zero-pidi-box/PIDI-BOX01-X-ZERO/FOTOS and 3D/3TE-displ-mounting1.jpg

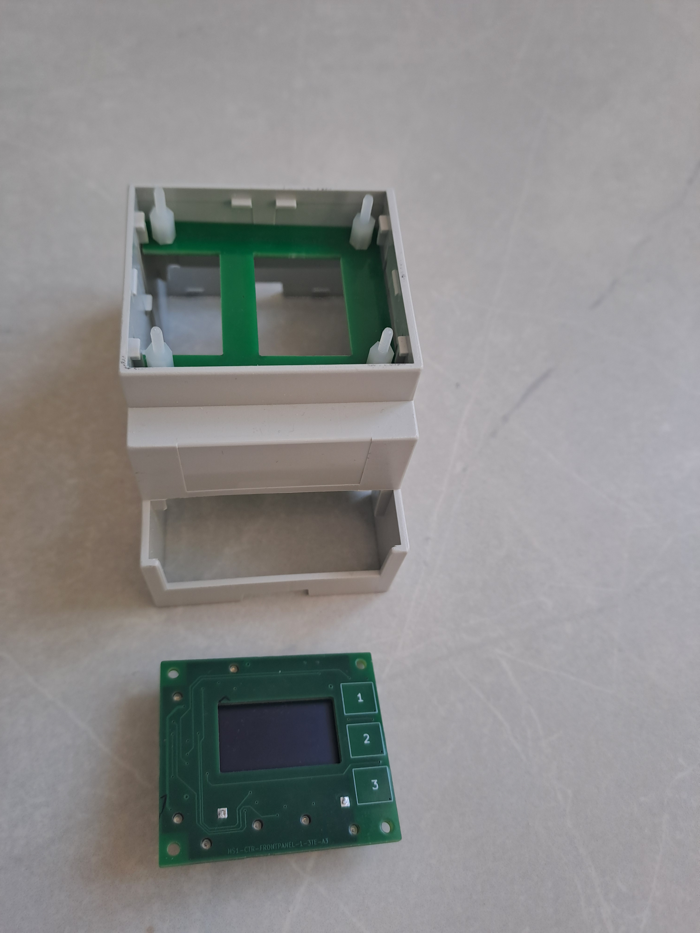
FOTOS and 3D/3TE-displ-mounting1.jpg
