zero-pidi-box/PIDI-BOX01-X-ZERO/FOTOS and 3D/3TE-displ-mounting 3.jpg

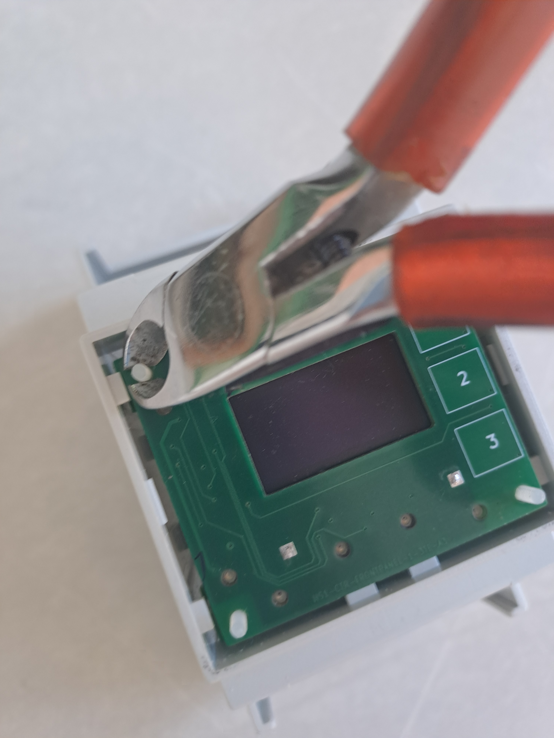
FOTOS and 3D/3TE-displ-mounting 3.jpg
