zero-pidi-box/PIDI-BOX01-X-ZERO/FOTOS and 3D/6 DIG-IN opto.jpg

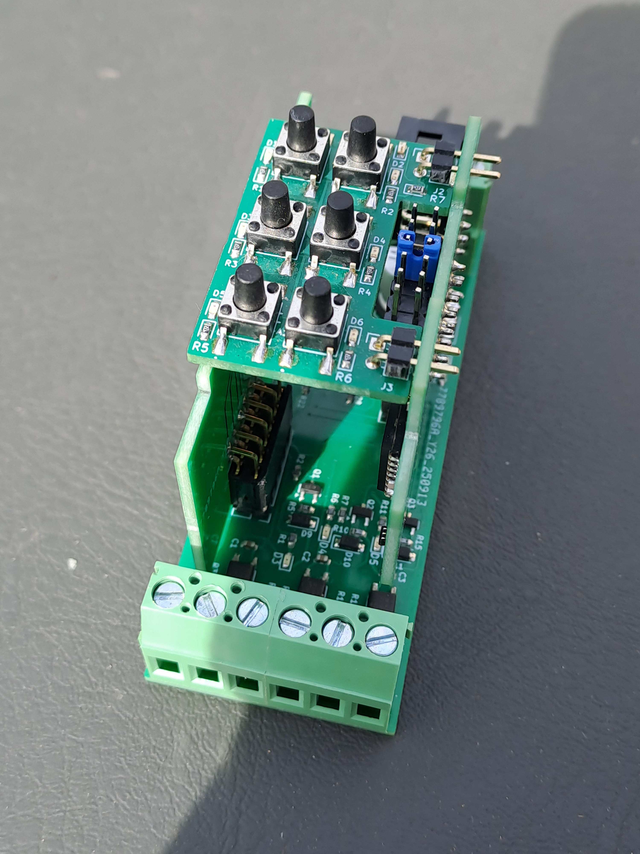
FOTOS and 3D/6 DIG-IN opto.jpg
