zero-pidi-box/PIDI-BOX01-X-ZERO/FOTOS and 3D/6 RELAYS OUT.jpg

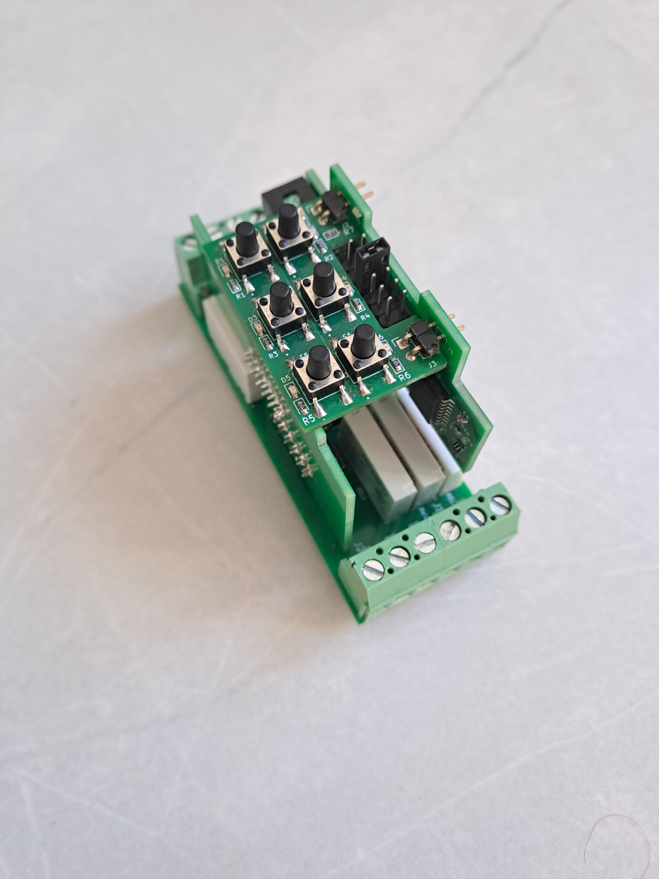
FOTOS and 3D/6 RELAYS OUT.jpg
