zero-pidi-box/PIDI-BOX01-X-ZERO/FOTOS and 3D/MOUNTING FRONTPLATE FRAME (1).jpg

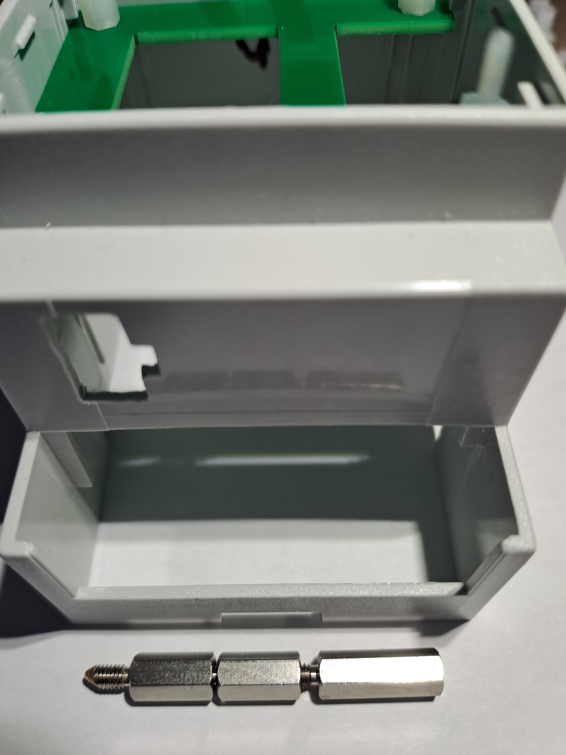
FOTOS and 3D/MOUNTING FRONTPLATE FRAME (1).jpg
