zero-pidi-box/PIDI-BOX01-X-ZERO/FOTOS and 3D/PIDI-6-IO-CONTOL.jpg

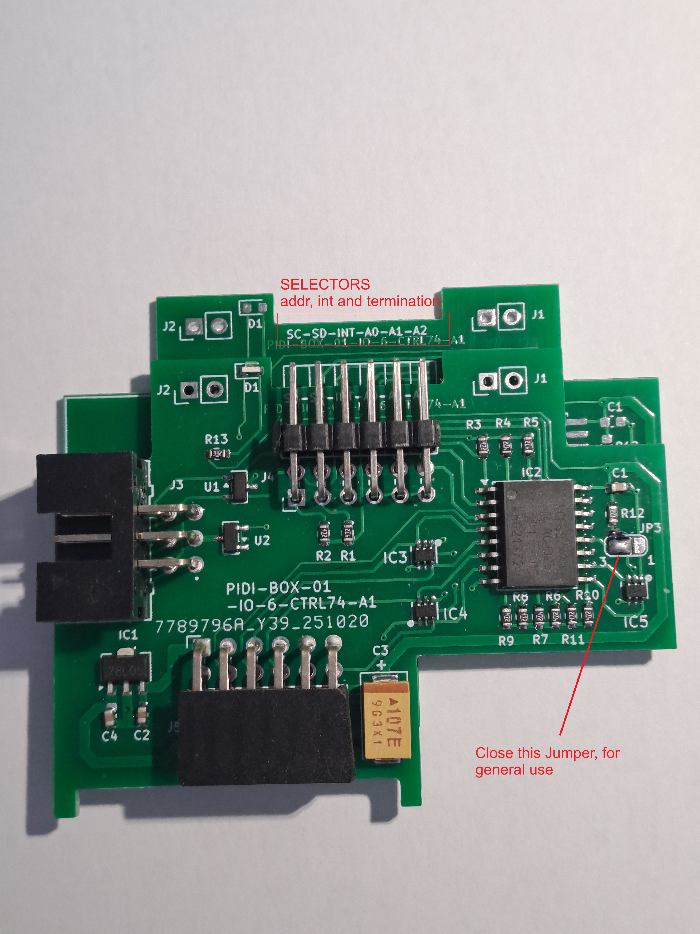
FOTOS and 3D/PIDI-6-IO-CONTOL.jpg
