zero-pidi-box/PIDI-BOX01-X-ZERO/FOTOS and 3D/PIDI-B01-CONTROL.jpg

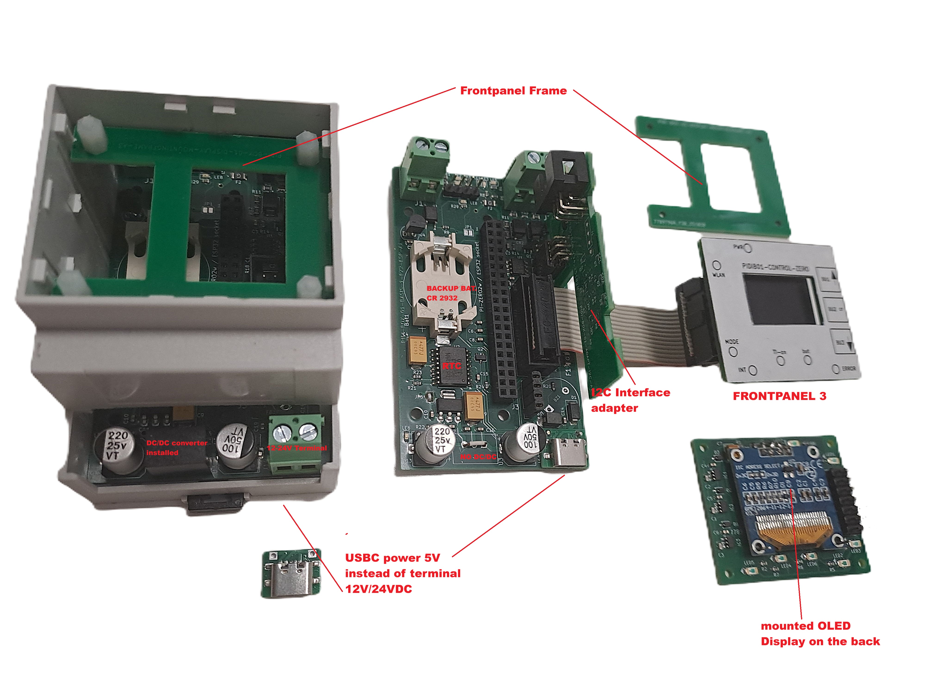
FOTOS and 3D/PIDI-B01-CONTROL.jpg
