zero-pidi-box/PIDI-BOX01-X-ZERO/FOTOS and 3D/PIDI-BOX-01-4 IN Analog ADS1115-A1.jpg

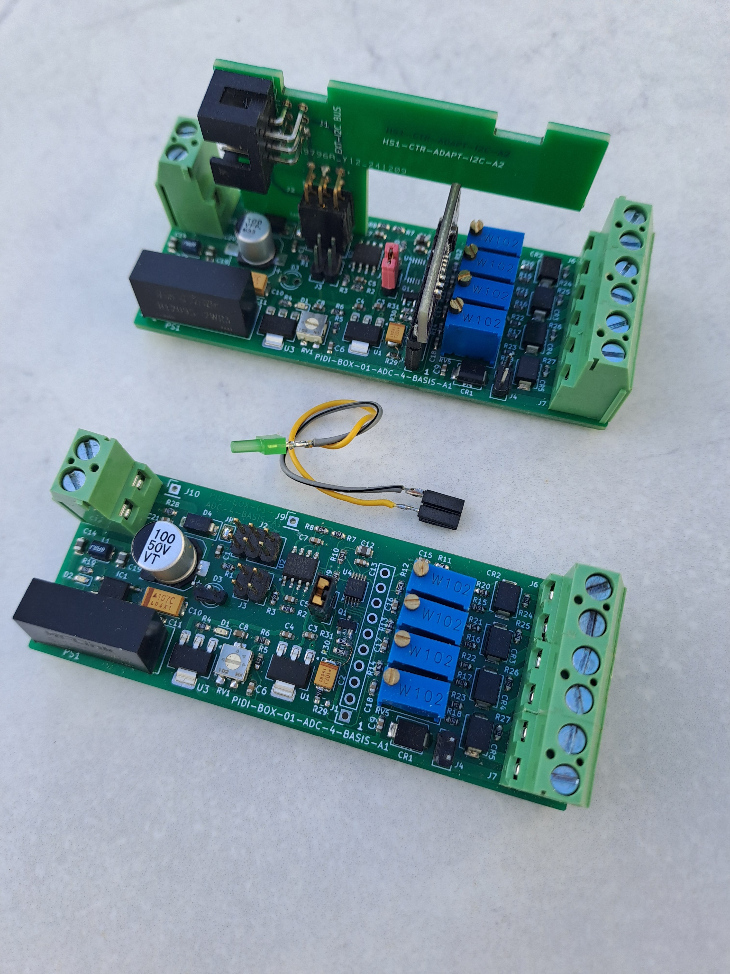
FOTOS and 3D/PIDI-BOX-01-4 IN Analog ADS1115-A1.jpg
