zero-pidi-box/PIDI-BOX01-X-ZERO/FOTOS and 3D/PIDI-BOX-01-ADC-4-MAIN-A1.jpg

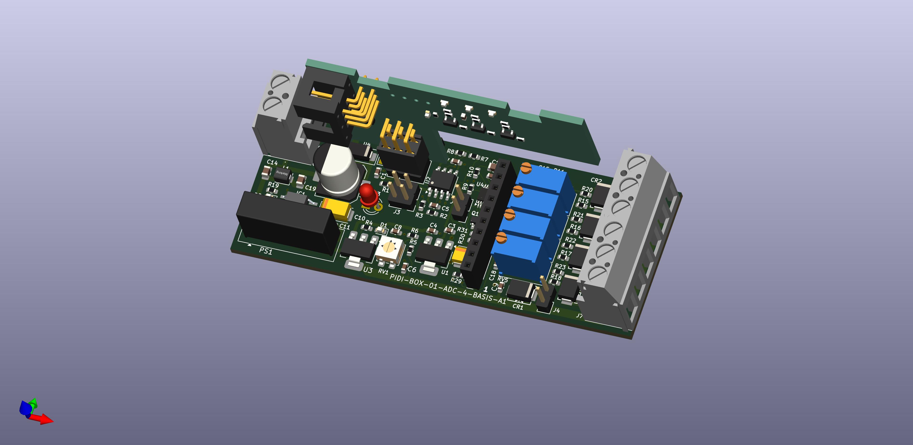
FOTOS and 3D/PIDI-BOX-01-ADC-4-MAIN-A1.jpg
