zero-pidi-box/PIDI-BOX01-X-ZERO/FOTOS and 3D/PIDI-BOX-01-ALL PCB's by JLCPCB.jpg

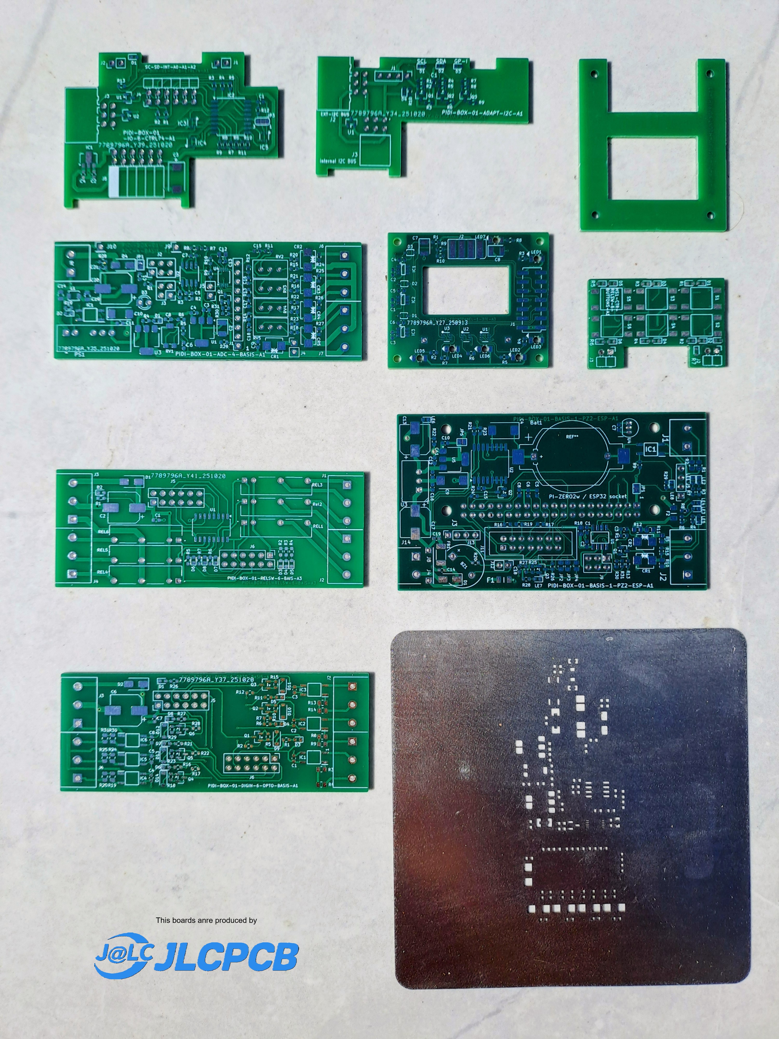
FOTOS and 3D/PIDI-BOX-01-ALL PCB's by JLCPCB.jpg
