zero-pidi-box/PIDI-BOX01-X-ZERO/FOTOS and 3D/PIDI-BOX-01-MAIN-1-PZ2_ESP-A1.jpg

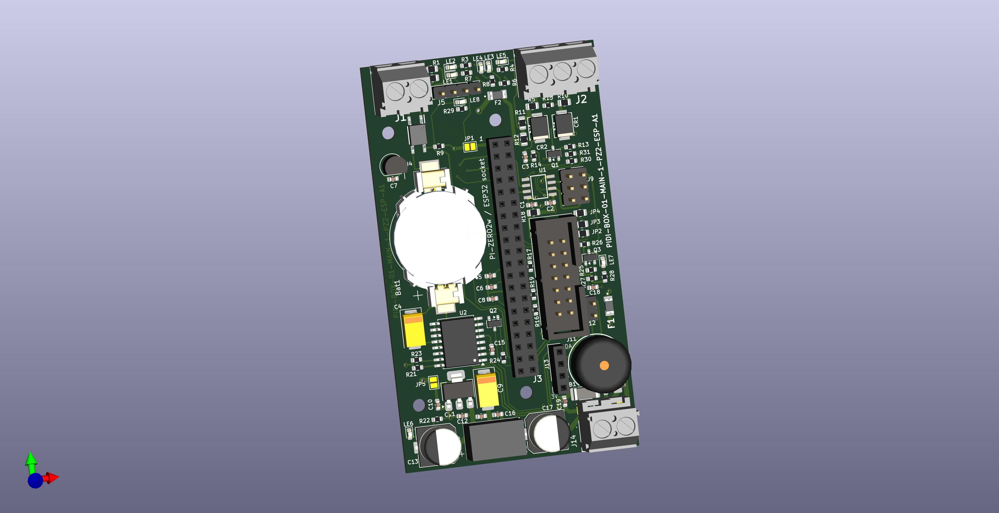
FOTOS and 3D/PIDI-BOX-01-MAIN-1-PZ2_ESP-A1.jpg
