zero-pidi-box/PIDI-BOX01-X-ZERO/FOTOS and 3D/SYSTEM example down side.jpg

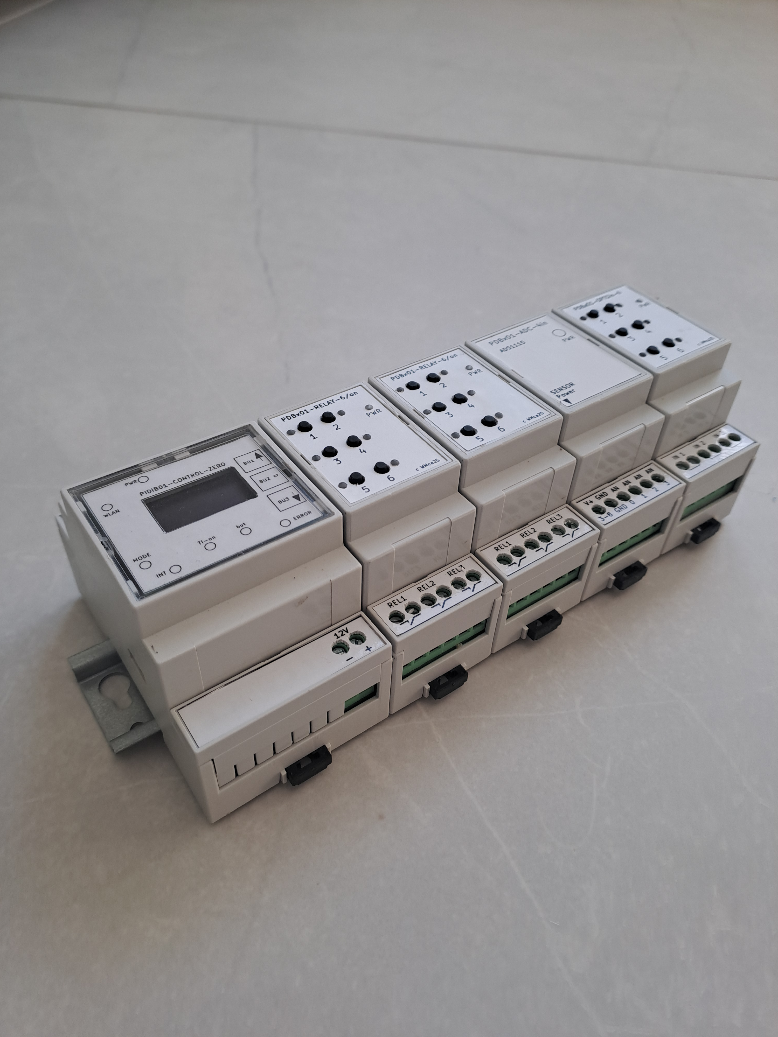
FOTOS and 3D/SYSTEM example down side.jpg
