zero-pidi-box/PIDI-BOX01-X-ZERO/FOTOS and 3D/SYSTEM example i2C-BUS-side.jpg

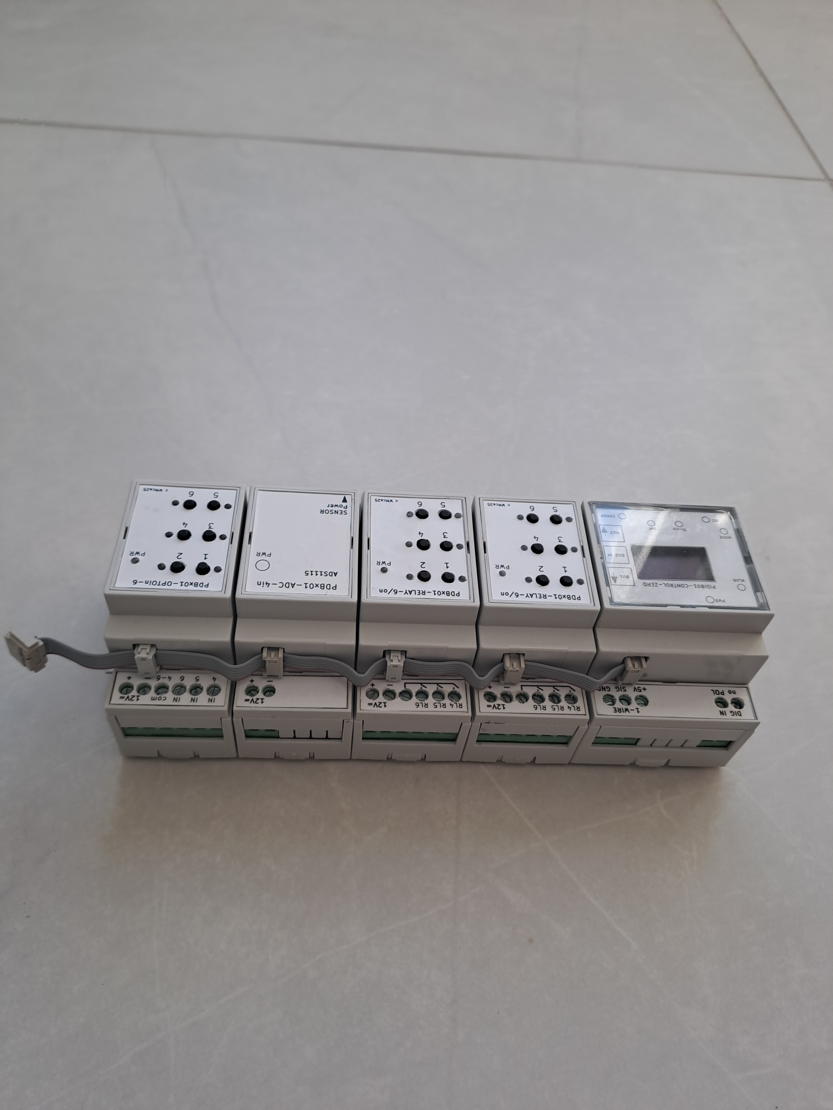
FOTOS and 3D/SYSTEM example i2C-BUS-side.jpg
