zero-pidi-box/PIDI-BOX01-X-ZERO/FOTOS and 3D/SYSTEM example top.jpg

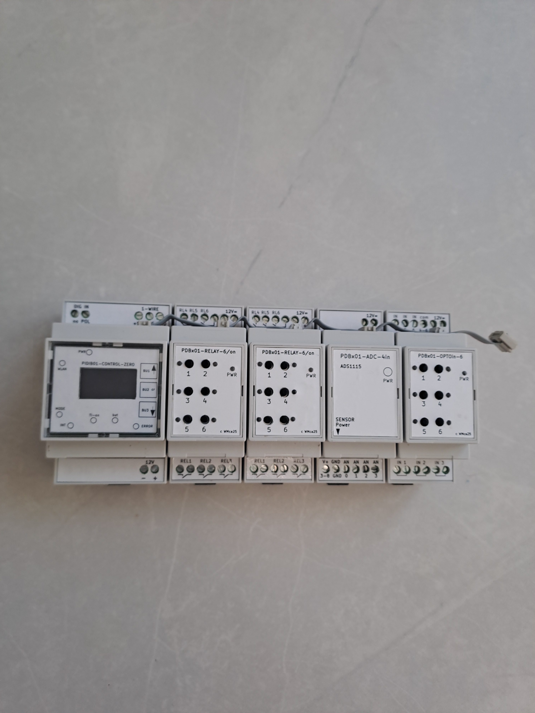
FOTOS and 3D/SYSTEM example top.jpg
