zero-pidi-box/PIDI-BOX01-X-ZERO/KICAD_BOARDS/PIDI-BOX-01-ADAPT-I2C-A1/PIDI-BOX-01-ADAPT-I2C-A1.jpg

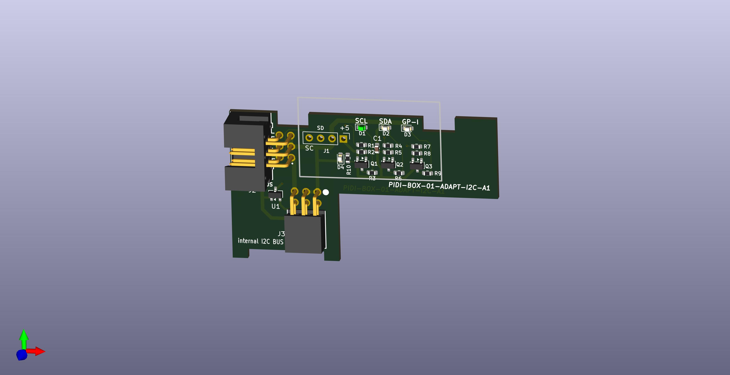
KICAD_BOARDS/PIDI-BOX-01-ADAPT-I2C-A1/PIDI-BOX-01-ADAPT-I2C-A1.jpg
