zero-pidi-box/PIDI-BOX01-X-ZERO/KICAD_BOARDS/PIDI-BOX-01-MAIN-1-PZ2-ESP-A1/PIDI-BOX-01-MAIN-1-PZ2_ESP-A1-ZERO-I2C.jpg

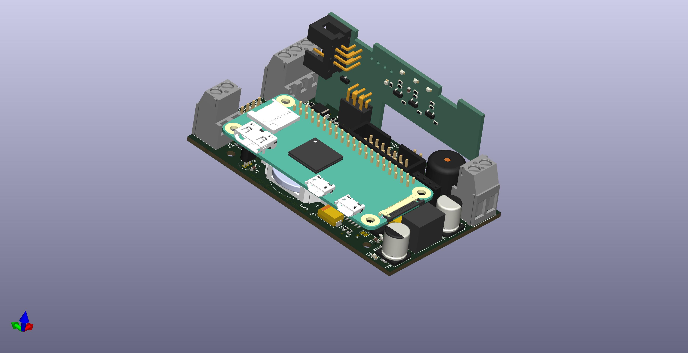
KICAD_BOARDS/PIDI-BOX-01-MAIN-1-PZ2-ESP-A1/PIDI-BOX-01-MAIN-1-PZ2_ESP-A1-ZERO-I2C.jpg
