zero-pidi-box/PIDI-BOX01-X-ZERO/KICAD_BOARDS/PIDI_specialparts_library/MYlib_GLOBAL_3dshapes/würth_12pol_613012243121.stp

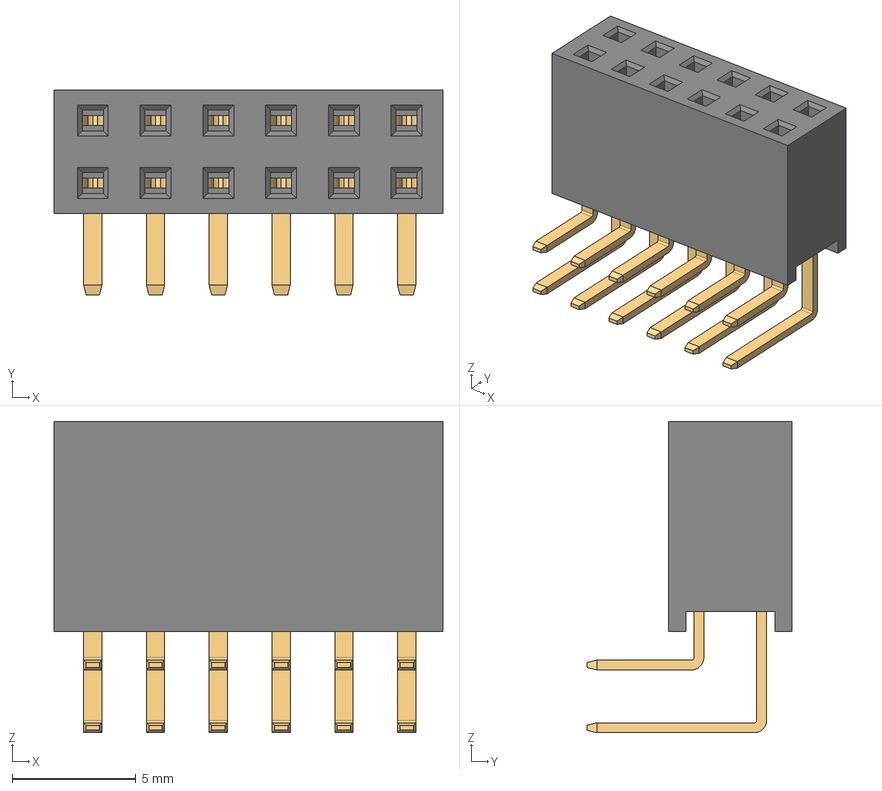
[picture p44: CAD file, 2026-02-07]
KICAD_BOARDS/PIDI_specialparts_library/MYlib_GLOBAL_3dshapes/würth_12pol_613012243121.stp
15.7 x 8.30 x 12.6 mm
6130xx243121_PIN x 6
6130xx243121_PIN_G x 6
