zero-pidi-box/PIDI-BOX01-X-ZERO/KICAD_BOARDS/PIDI_specialparts_library/MYlib_GLOBAL_3dshapes/L_Wurth_WE-GF-3225.step

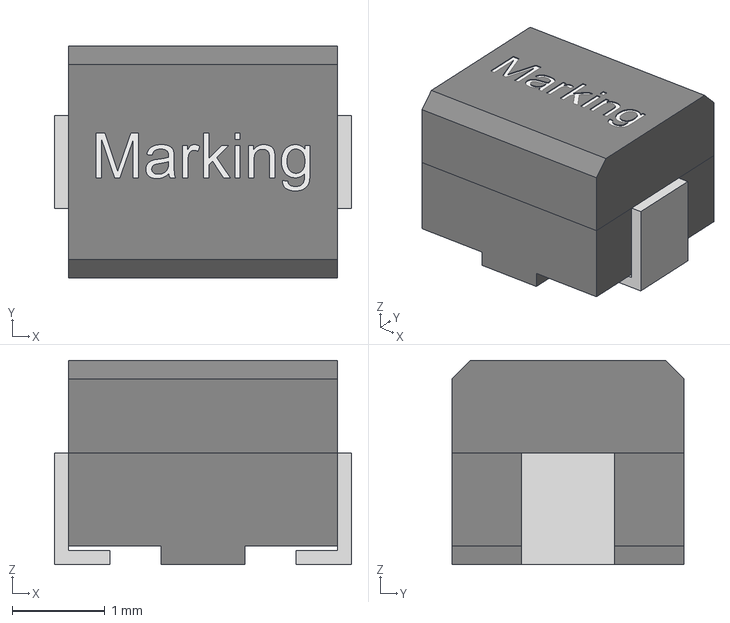
[picture p45: CAD file, 2026-02-07]
KICAD_BOARDS/PIDI_specialparts_library/MYlib_GLOBAL_3dshapes/L_Wurth_WE-GF-3225.step
3.20 x 2.50 x 2.20 mm
