zero-pidi-box/PIDI-BOX01-X-ZERO/KICAD_BOARDS/PIDI_specialparts_library/MYlib_GLOBAL_3dshapes/SW_tactile-6X6_smd.stp

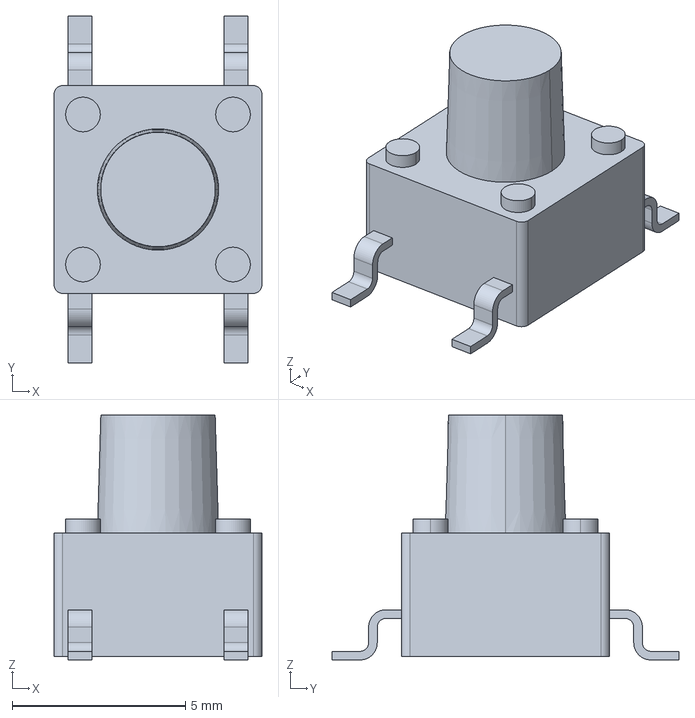
[picture p46: CAD file, 2026-02-07]
KICAD_BOARDS/PIDI_specialparts_library/MYlib_GLOBAL_3dshapes/SW_tactile-6X6_smd.stp
6.00 x 10.0 x 7.07 mm
