zero-pidi-box/PIDI-BOX01-X-ZERO/KICAD_BOARDS/PIDI_specialparts_library/MYlib_GLOBAL_3dshapes/BU2032SM-BT-GTR.STEP

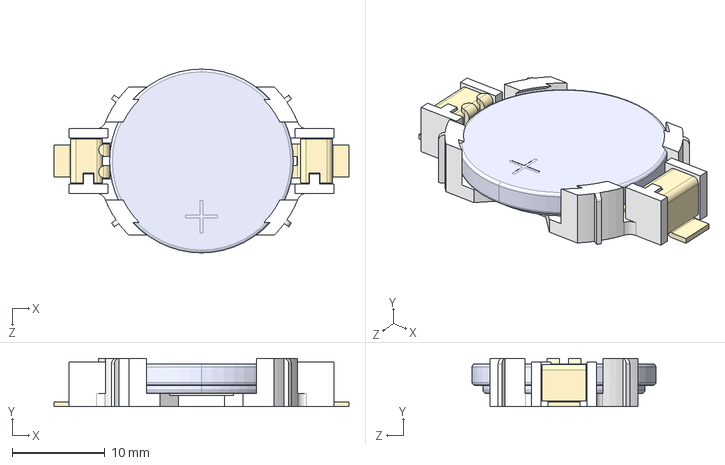
[picture p47: CAD file, 2026-02-07]
KICAD_BOARDS/PIDI_specialparts_library/MYlib_GLOBAL_3dshapes/BU2032SM-BT-GTR.STEP
31.9 x 5.20 x 19.9 mm
