zero-pidi-box/PIDI-BOX01-X-ZERO/KICAD_BOARDS/PIDI_specialparts_library/MYlib_GLOBAL_3dshapes/L_Wurth_WE-GF-4532.step

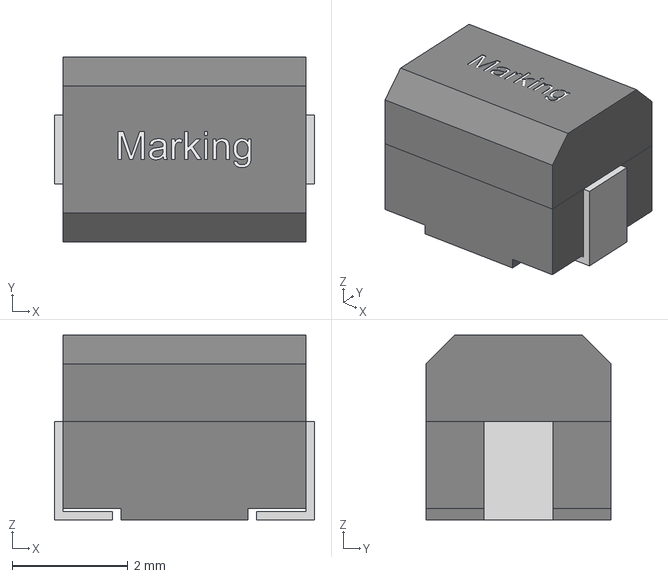
[picture p48: CAD file, 2026-02-07]
KICAD_BOARDS/PIDI_specialparts_library/MYlib_GLOBAL_3dshapes/L_Wurth_WE-GF-4532.step
4.50 x 3.20 x 3.20 mm
