zero-pidi-box/PIDI-BOX01-X-ZERO/KICAD_BOARDS/PIDI_specialparts_library/MYlib_GLOBAL_3dshapes/würth_6pol_613006243121.stp

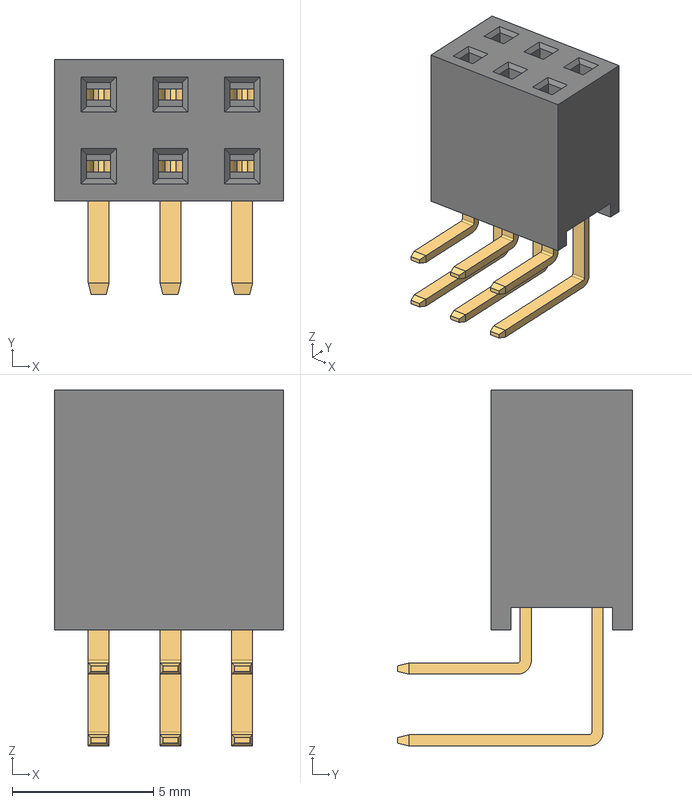
[picture p52: CAD file, 2026-02-07]
KICAD_BOARDS/PIDI_specialparts_library/MYlib_GLOBAL_3dshapes/würth_6pol_613006243121.stp
8.12 x 8.30 x 12.6 mm
6130xx243121_PIN x 3
6130xx243121_PIN_G x 3
